whowechina/musec_pico/References/a-relic-of-the-past-museca-v0-1a24ue6pef9d1.webp

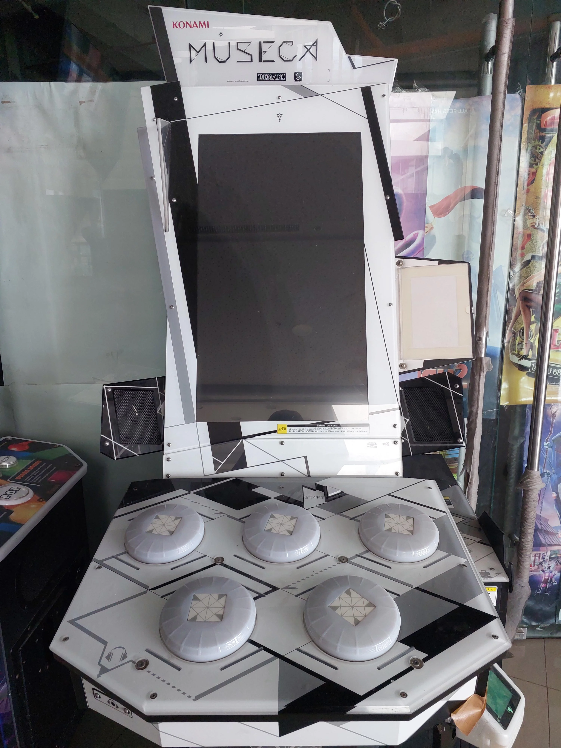
References/a-relic-of-the-past-museca-v0-1a24ue6pef9d1.webp
