whowechina/musec_pico/References/a-relic-of-the-past-museca-v0-k1ehcvuoef9d1.webp

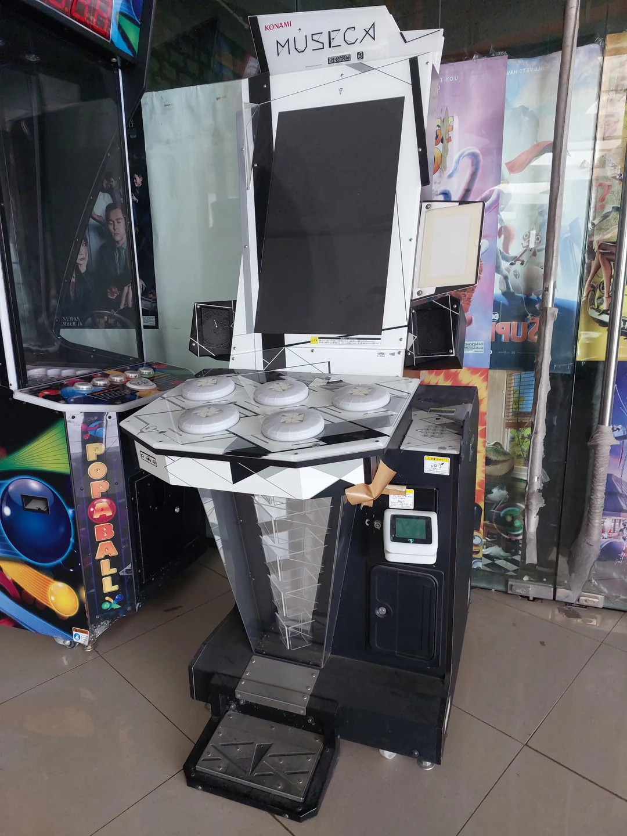
References/a-relic-of-the-past-museca-v0-k1ehcvuoef9d1.webp
