whowechina/musec_pico/References/museca-1.jpg

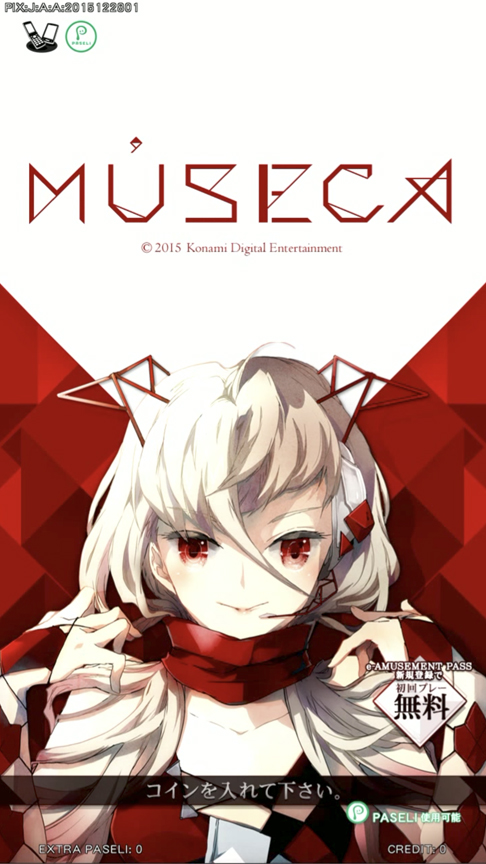
References/museca-1.jpg
