whowechina/musec_pico/Production/3DPrint/musec_pico+_pad.stl

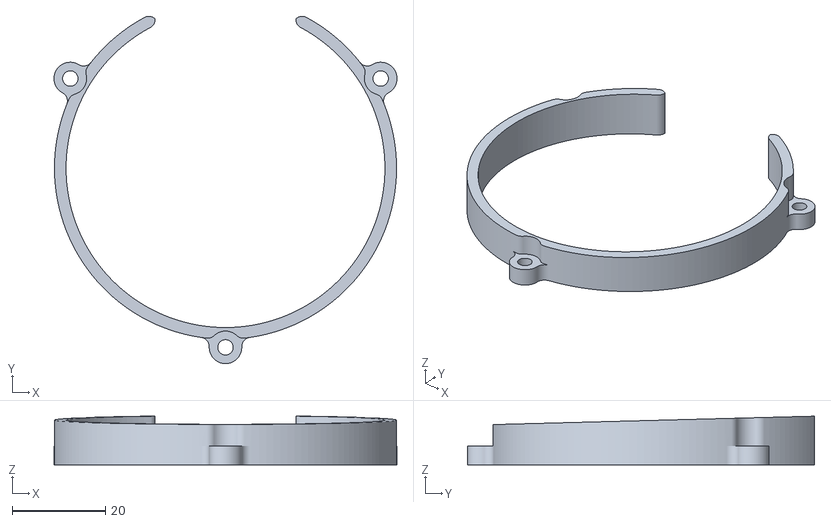
[picture p44: CAD file, 2025-05-17]
Production/3DPrint/musec_pico+_pad.stl
73.7 x 74.6 x 10.5
