whowechina/musec_pico/Production/3DPrint/musec_pico_bottom.stl

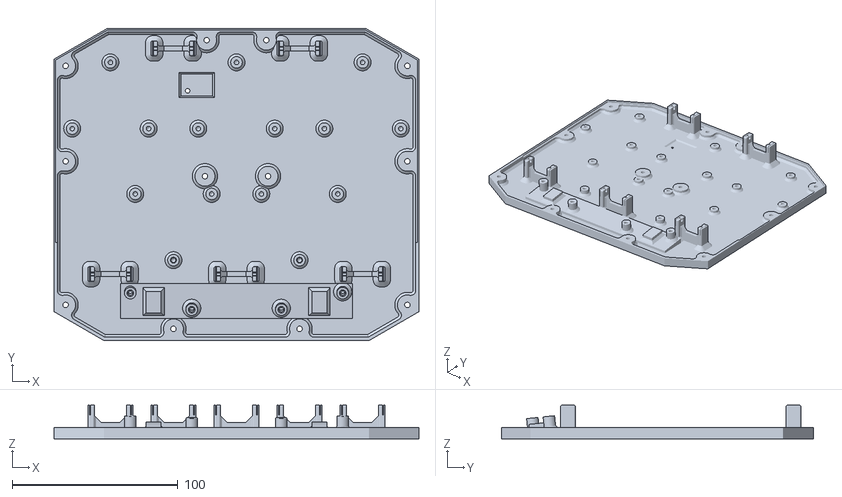
[picture p45: CAD file, 2024-10-18]
Production/3DPrint/musec_pico_bottom.stl
220.0 x 188.0 x 20.4
