whowechina/musec_pico/PCB/plus/3dmodels/SKPMAM.STEP

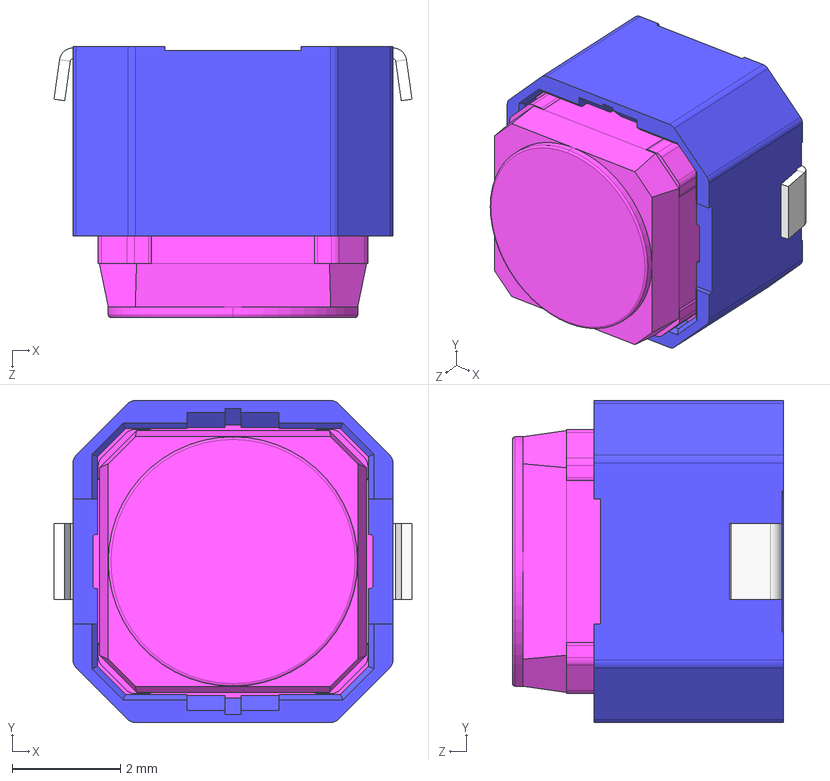
[picture p46: CAD file, 2025-05-04]
PCB/plus/3dmodels/SKPMAM.STEP
6.60 x 5.94 x 5.00 mm
