whowechina/musec_pico/Production/3DPrint/musec_pico_aux.stl

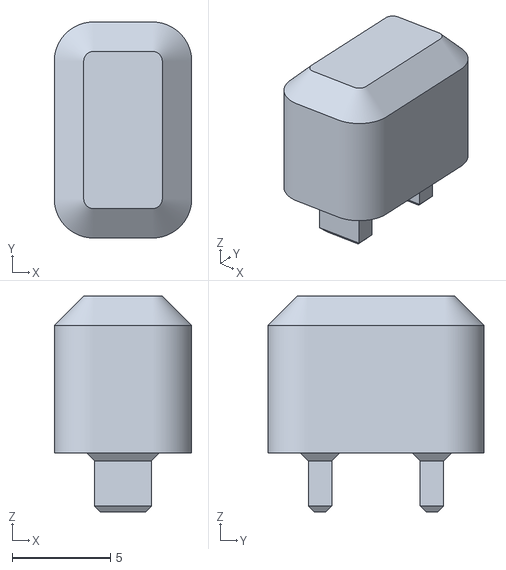
[picture p47: CAD file, 2024-10-16]
Production/3DPrint/musec_pico_aux.stl
7.00 x 11.0 x 11.0
