whowechina/musec_pico/PCB/plus/3dmodels/mpr121_breakout_v13.stl

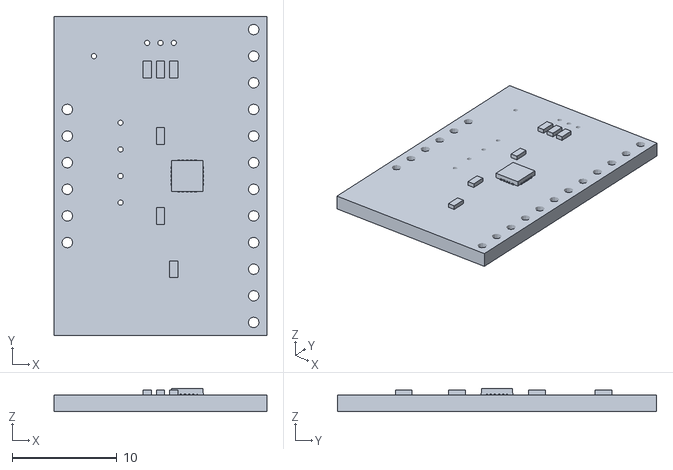
[picture p48: CAD file, 2025-05-04]
PCB/plus/3dmodels/mpr121_breakout_v13.stl
20.3 x 30.5 x 2.20
