whowechina/musec_pico/Production/3DPrint/musec_pico_shaft_end_7mm.stl

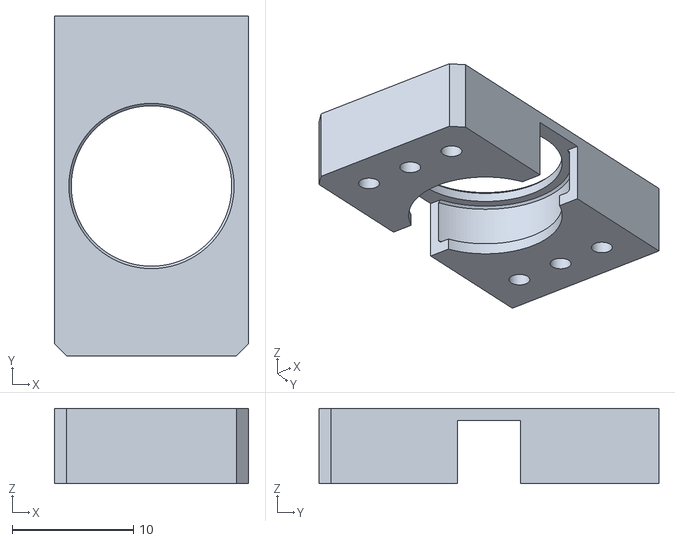
[picture p49: CAD file, 2024-10-16]
Production/3DPrint/musec_pico_shaft_end_7mm.stl
16.0 x 28.0 x 6.20
