whowechina/musec_pico/PCB/plus/3dmodels/EVQ-P1D05M.stp

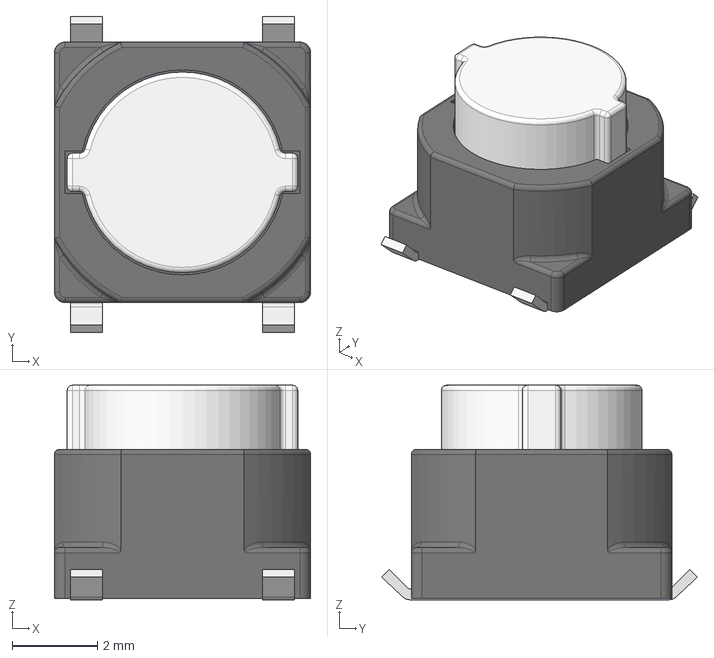
[picture p50: CAD file, 2025-05-04]
PCB/plus/3dmodels/EVQ-P1D05M.stp
6.00 x 7.40 x 5.03 mm
