whowechina/musec_pico/Production/3DPrint/musec_pico_shaft_end_6mm.stl

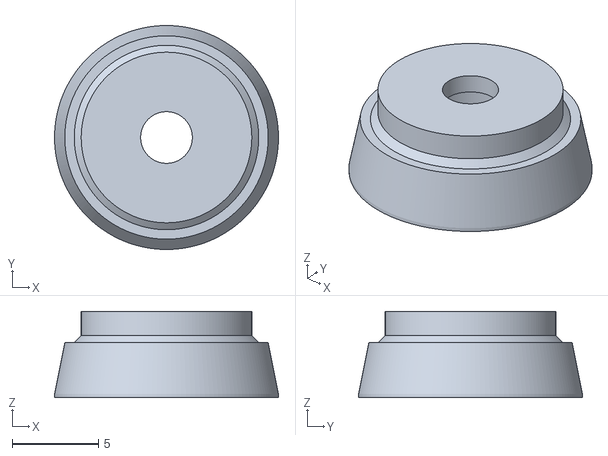
[picture p51: CAD file, 2024-10-16]
Production/3DPrint/musec_pico_shaft_end_6mm.stl
13.0 x 13.0 x 5.00
