whowechina/musec_pico/Production/3DPrint/musec_pico_pedal.stl

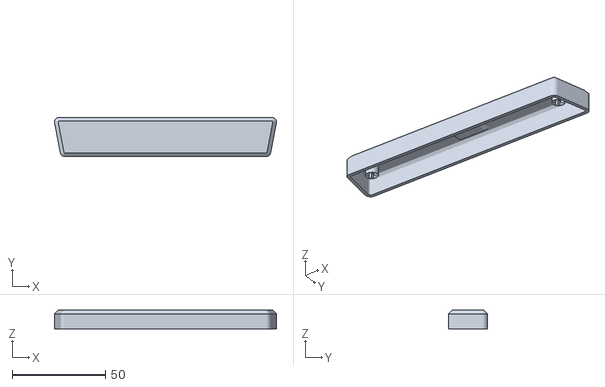
[picture p53: CAD file, 2024-10-16]
Production/3DPrint/musec_pico_pedal.stl
119.0 x 21.0 x 10.0
