whowechina/musec_pico/PCB/plus/3dmodels/SKSTAAE010.stp

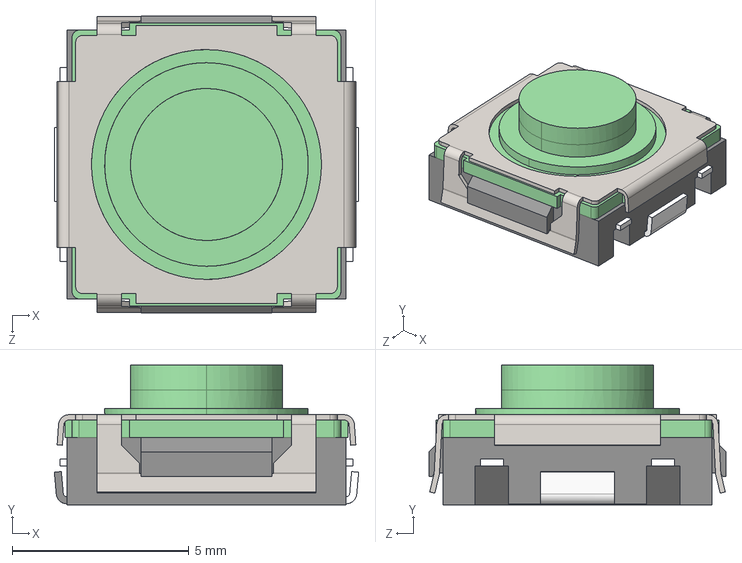
[picture p54: CAD file, 2025-05-04]
PCB/plus/3dmodels/SKSTAAE010.stp
8.61 x 3.95 x 8.40 mm
