whowechina/musec_pico/PCB/plus/3dmodels/Kailh_PG1353.STEP

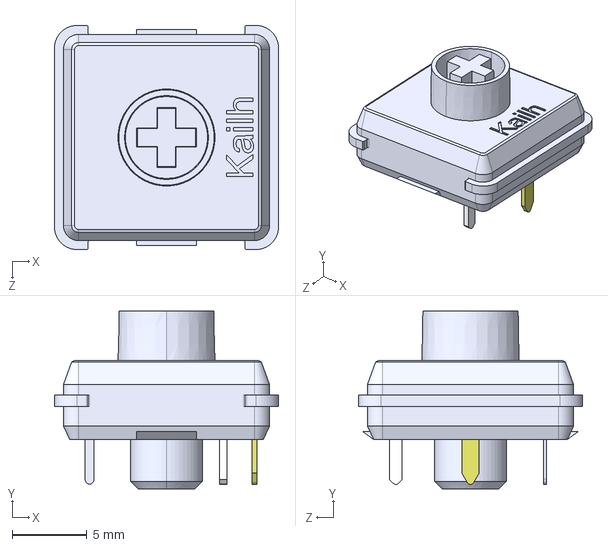
[picture p55: CAD file, 2025-05-04]
PCB/plus/3dmodels/Kailh_PG1353.STEP
15.0 x 11.9 x 15.0 mm
