whowechina/musec_pico/PCB/plus/3dmodels/User Library-RGB1204.STEP

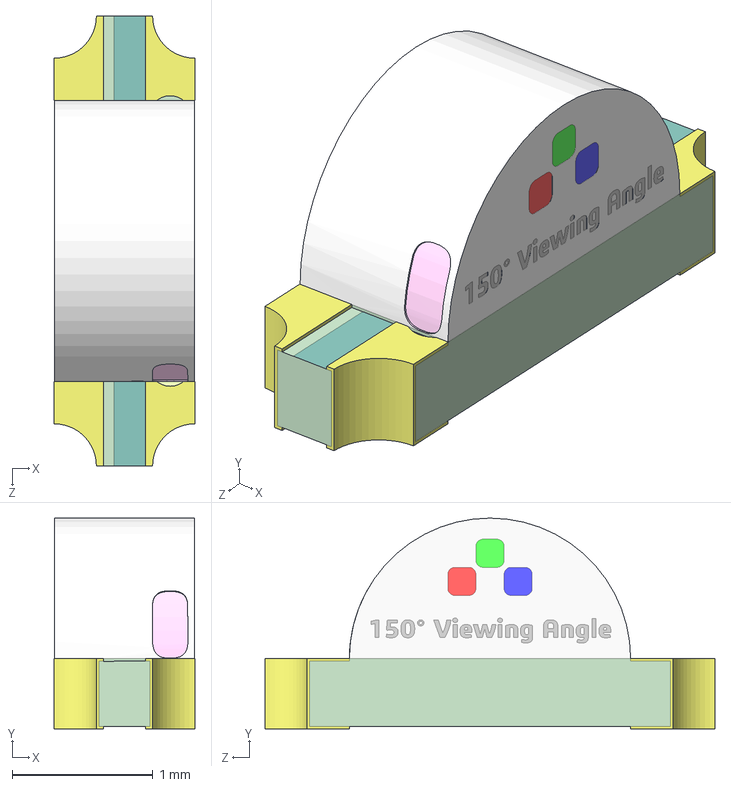
[picture p56: CAD file, 2025-05-04]
PCB/plus/3dmodels/User Library-RGB1204.STEP
1.00 x 1.50 x 3.20 mm
