whowechina/musec_pico/PCB/plus/3dmodels/SW_Hotswap_Kailh_Choc_V1.stp

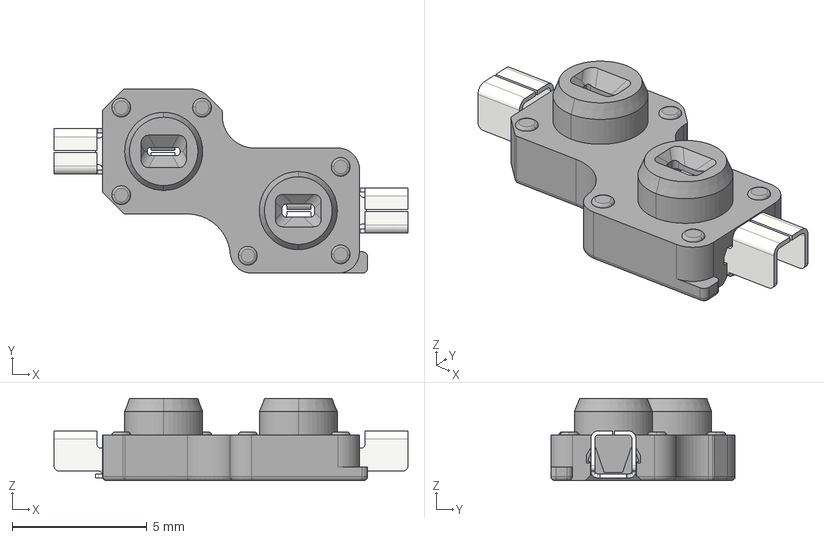
[picture p57: CAD file, 2024-09-26]
PCB/plus/3dmodels/SW_Hotswap_Kailh_Choc_V1.stp
13.2 x 6.85 x 3.05 mm
