whowechina/musec_pico/PCB/plus/3dmodels/keypad_lgp.3mf

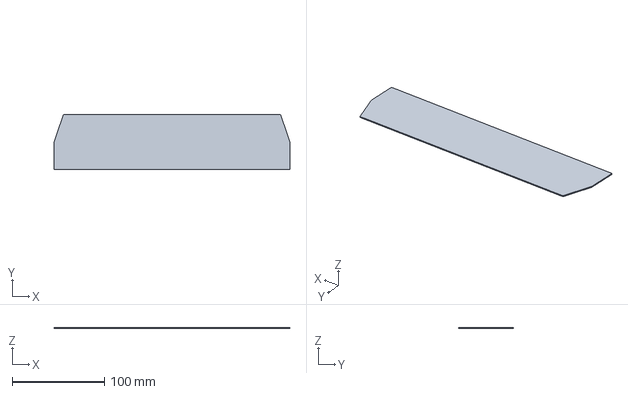
[picture p58: CAD file, 2024-09-26]
PCB/plus/3dmodels/keypad_lgp.3mf
256.0 x 60.0 x 1.00 mm
