whowechina/musec_pico/PCB/plus/3dmodels/Magnetic Pogo Connector 5 Pin (Type 2).STEP

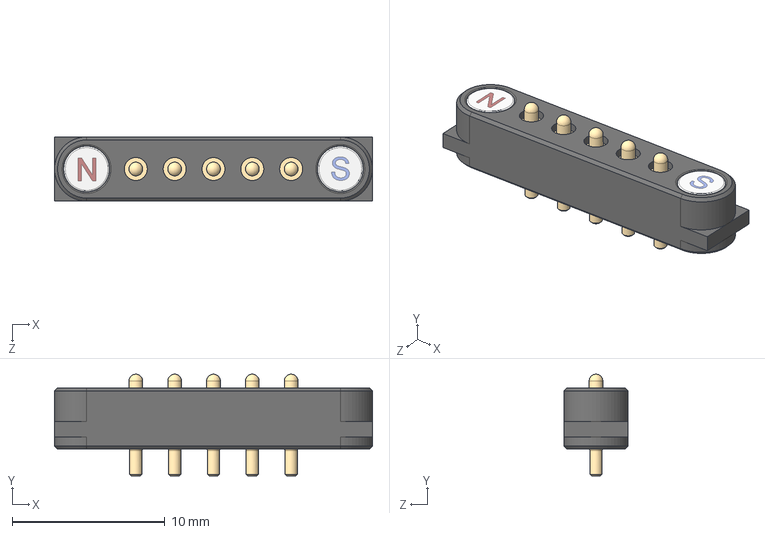
[picture p59: CAD file, 2024-09-26]
PCB/plus/3dmodels/Magnetic Pogo Connector 5 Pin (Type 2).STEP
20.8 x 6.65 x 4.20 mm
