whowechina/musec_pico/PCB/plus/3dmodels/Magnetic Pogo Connector 5 Pin (Type 3).STEP

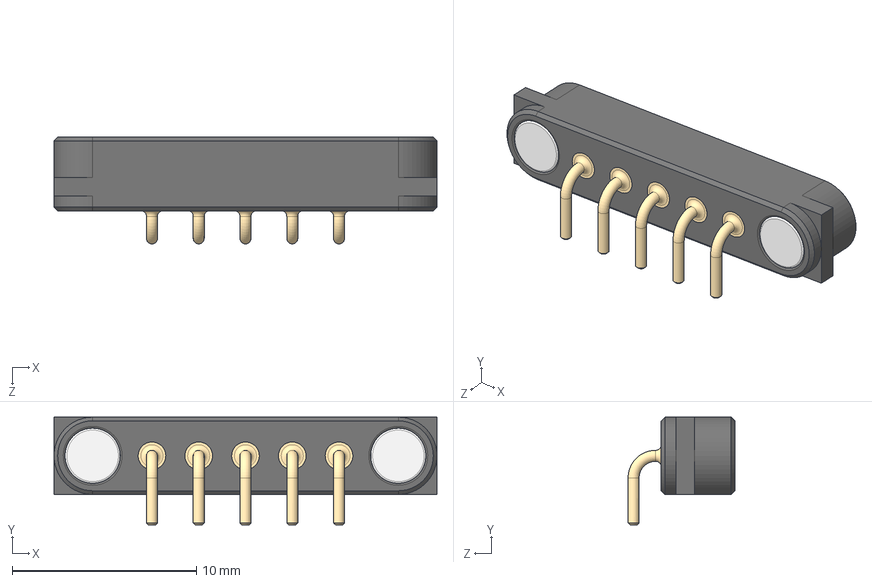
[picture p60: CAD file, 2024-09-26]
PCB/plus/3dmodels/Magnetic Pogo Connector 5 Pin (Type 3).STEP
20.8 x 5.85 x 5.80 mm
