whowechina/musec_pico/PCB/plus/3dmodels/SW_Kailh_Choc_V1.stp

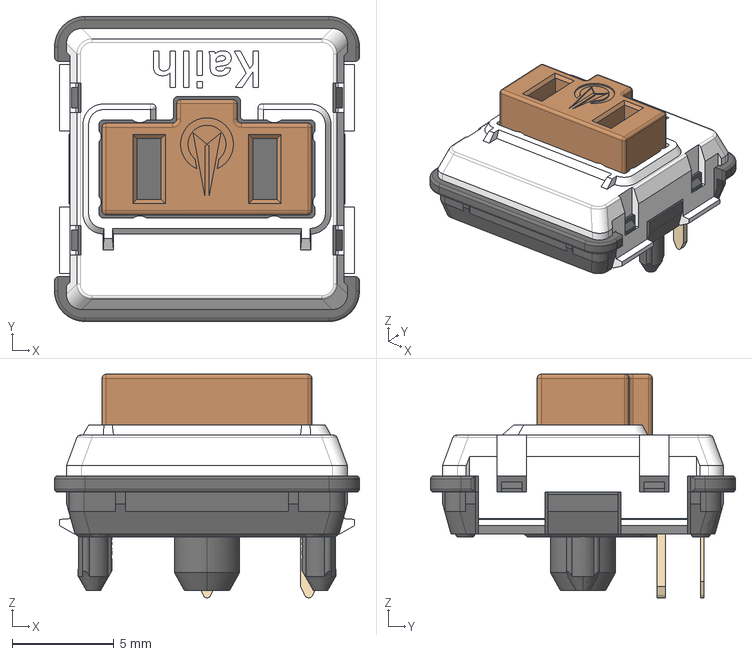
[picture p61: CAD file, 2024-09-26]
PCB/plus/3dmodels/SW_Kailh_Choc_V1.stp
15.0 x 15.0 x 11.0 mm
