whowechina/musec_pico/PCB/plus/3dmodels/8002A.step

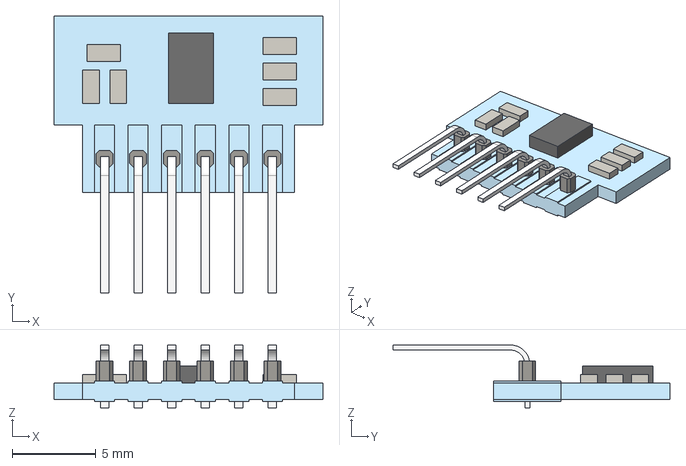
[picture p62: CAD file, 2024-09-26]
PCB/plus/3dmodels/8002A.step
16.0 x 16.5 x 3.75 mm
