whowechina/musec_pico/PCB/plus/3dmodels/WS2812B.step

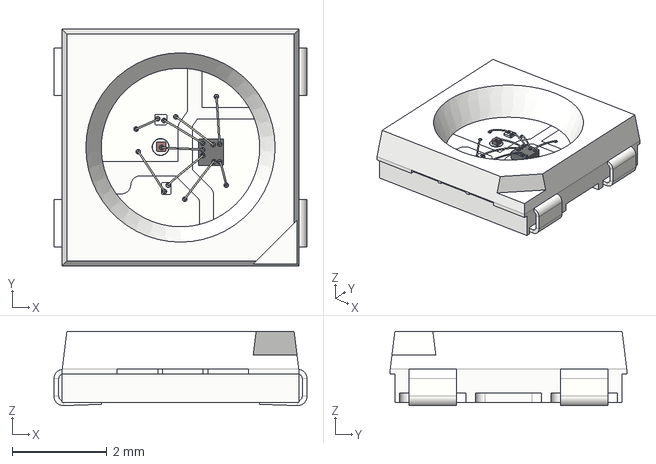
[picture p63: CAD file, 2024-09-26]
PCB/plus/3dmodels/WS2812B.step
5.35 x 5.00 x 1.57 mm
