whowechina/musec_pico/PCB/plus/3dmodels/geki_button.step

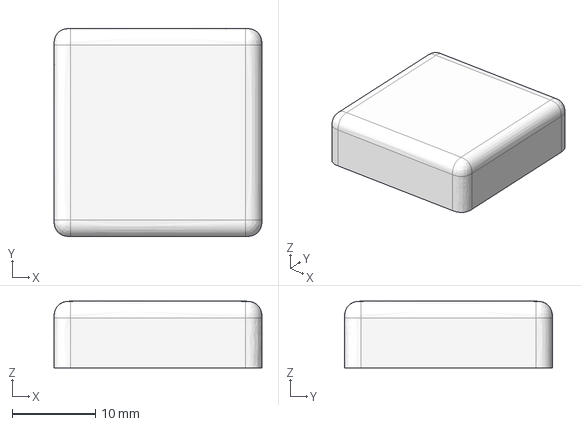
[picture p64: CAD file, 2024-09-26]
PCB/plus/3dmodels/geki_button.step
25.0 x 25.0 x 8.00 mm
