whowechina/musec_pico/PCB/plus/3dmodels/chu_keypad_lgp.step

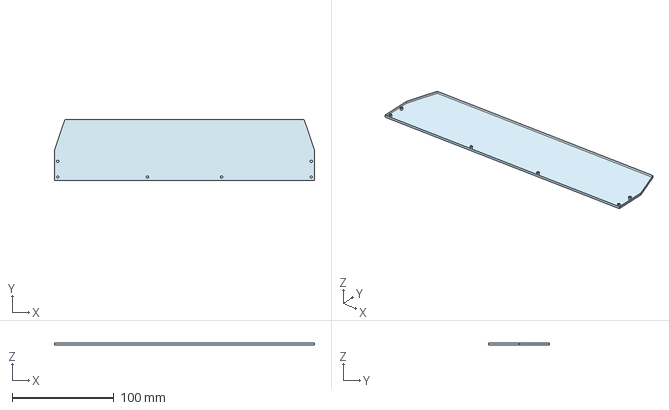
[picture p65: CAD file, 2024-09-26]
PCB/plus/3dmodels/chu_keypad_lgp.step
256.0 x 60.0 x 2.00 mm
