whowechina/musec_pico/PCB/plus/3dmodels/dcdc_3to5.step

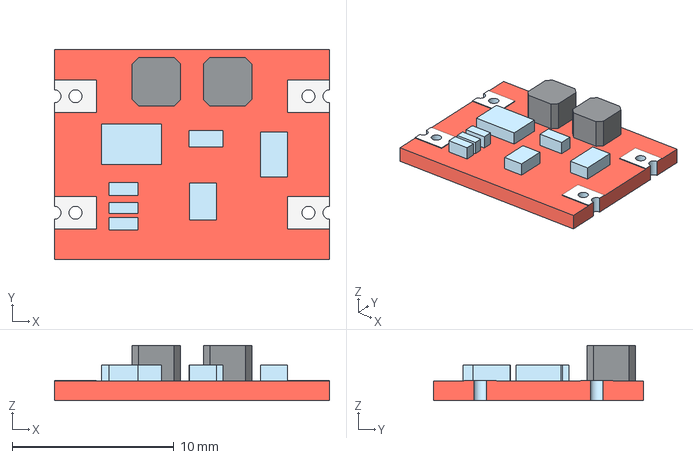
[picture p66: CAD file, 2024-09-26]
PCB/plus/3dmodels/dcdc_3to5.step
17.0 x 13.0 x 3.40 mm
