whowechina/musec_pico/PCB/plus/3dmodels/WS2812-2020.STEP

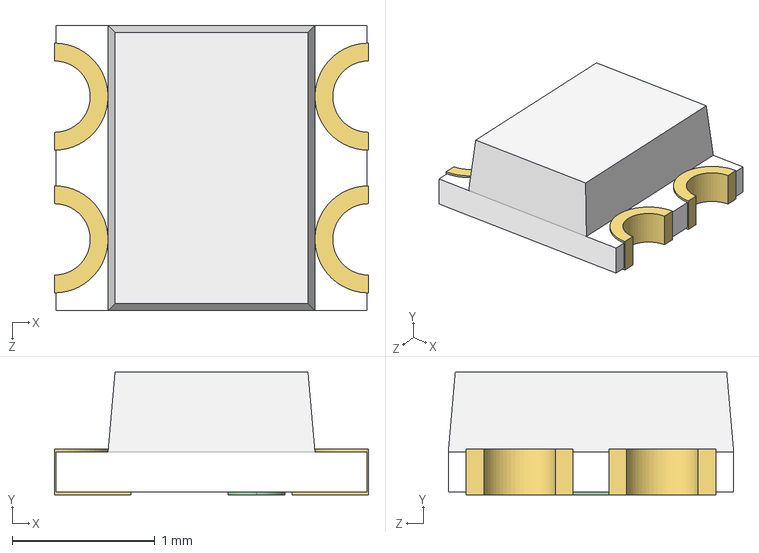
[picture p67: CAD file, 2024-09-26]
PCB/plus/3dmodels/WS2812-2020.STEP
2.20 x 0.86 x 2.00 mm
