whowechina/musec_pico/PCB/plus/3dmodels/J 2835.step

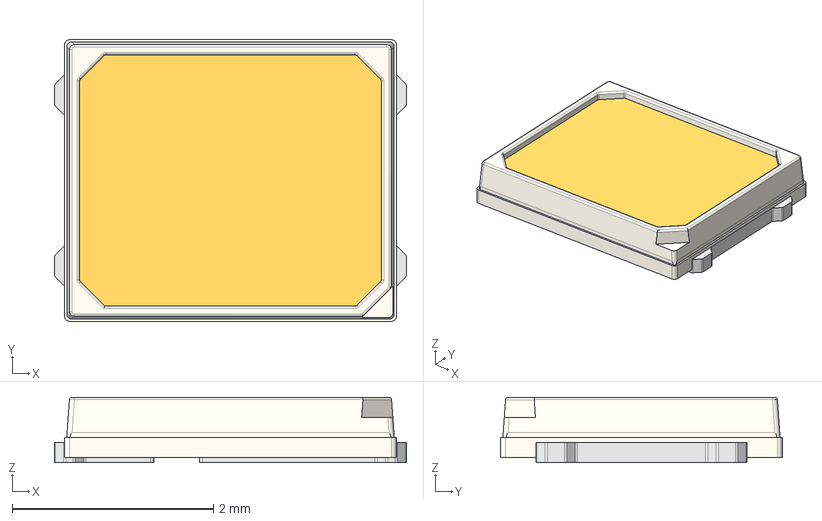
[picture p68: CAD file, 2024-09-26]
PCB/plus/3dmodels/J 2835.step
3.50 x 2.80 x 0.65 mm
