whowechina/musec_pico/PCB/plus/3dmodels/Kailh LP Choc PC Keycap.step

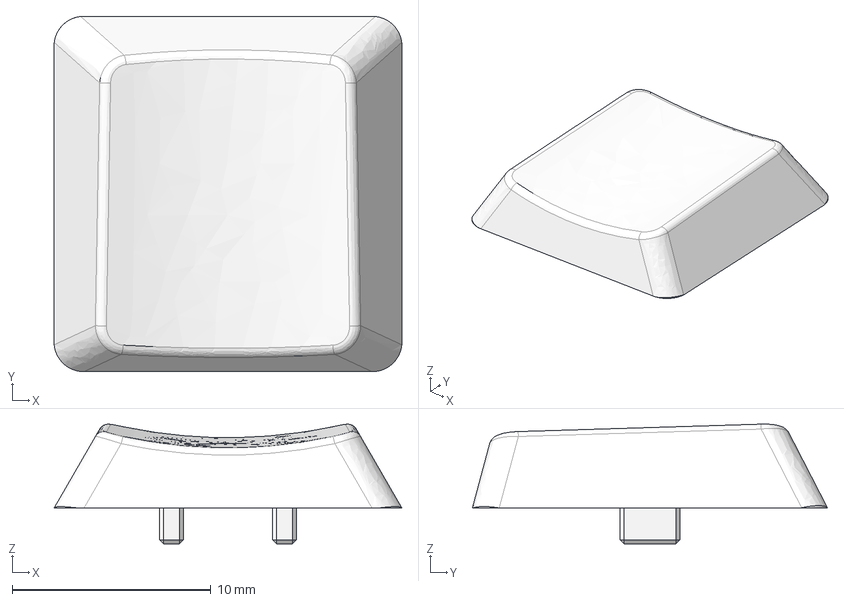
[picture p70: CAD file, 2024-09-26]
PCB/plus/3dmodels/Kailh LP Choc PC Keycap.step
17.5 x 17.9 x 6.03 mm
