whowechina/musec_pico/PCB/plus/3dmodels/SW_Hotswap_Kailh_MX.stp

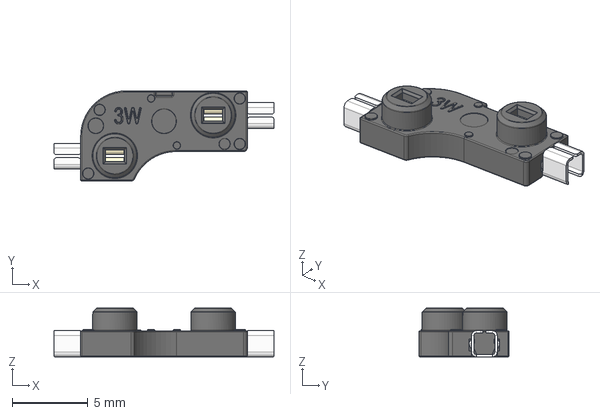
[picture p71: CAD file, 2024-09-26]
PCB/plus/3dmodels/SW_Hotswap_Kailh_MX.stp
14.5 x 5.95 x 3.22 mm
