whowechina/musec_pico/PCB/plus/3dmodels/Magnetic Pogo Connector 5 Pin (F).STEP

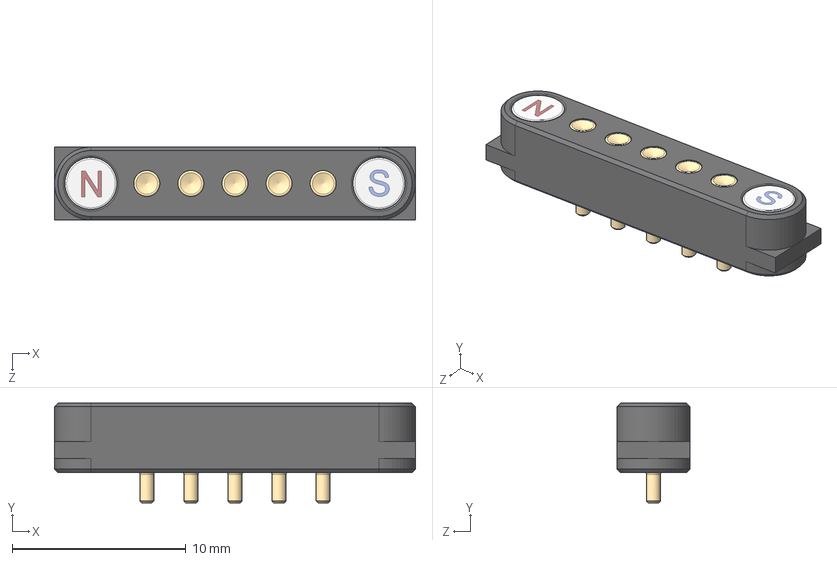
[picture p73: CAD file, 2024-09-26]
PCB/plus/3dmodels/Magnetic Pogo Connector 5 Pin (F).STEP
20.8 x 5.75 x 4.20 mm
