whowechina/musec_pico/PCB/plus/3dmodels/Tact Switch 4.5mm SMT.step

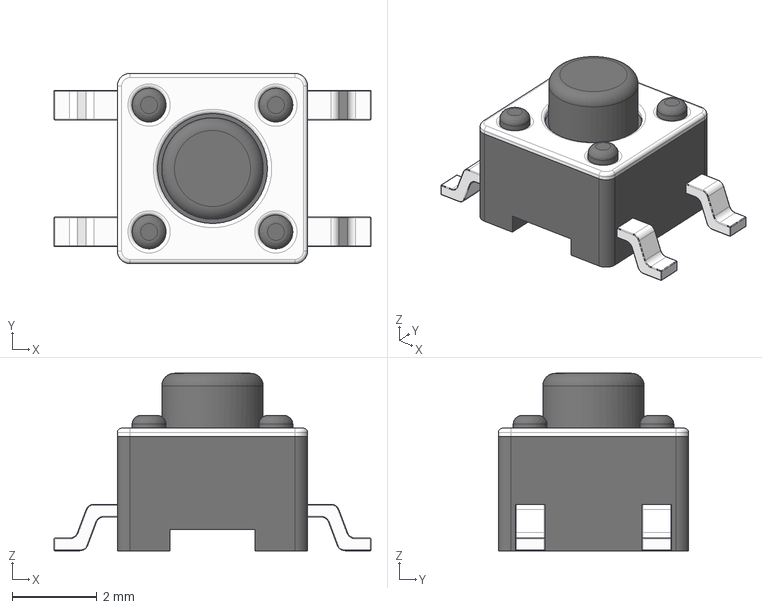
[picture p74: CAD file, 2024-09-26]
PCB/plus/3dmodels/Tact Switch 4.5mm SMT.step
7.50 x 4.50 x 4.20 mm
