whowechina/musec_pico/PCB/plus/3dmodels/SS49E.step

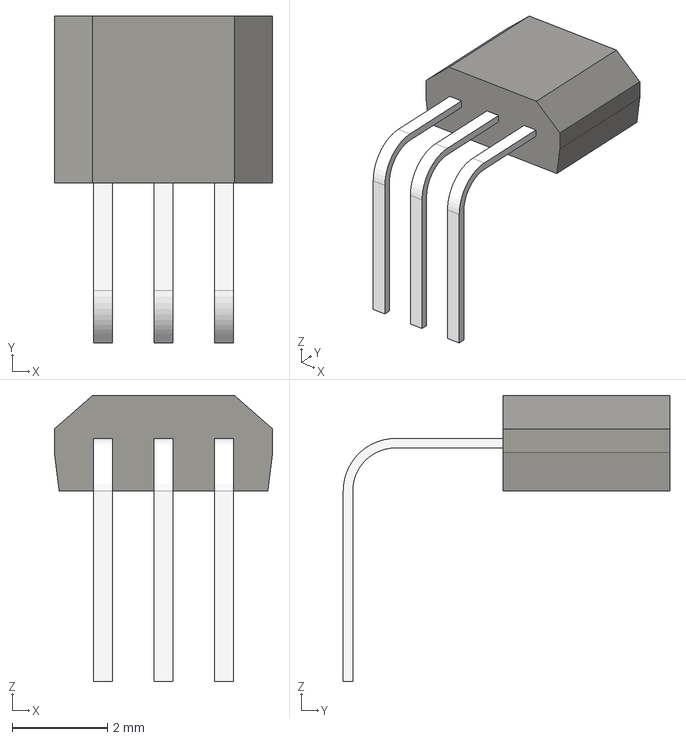
[picture p75: CAD file, 2024-09-26]
PCB/plus/3dmodels/SS49E.step
4.58 x 6.85 x 6.00 mm
