whowechina/musec_pico/PCB/plus/3dmodels/User Library-WS2812-2020.step

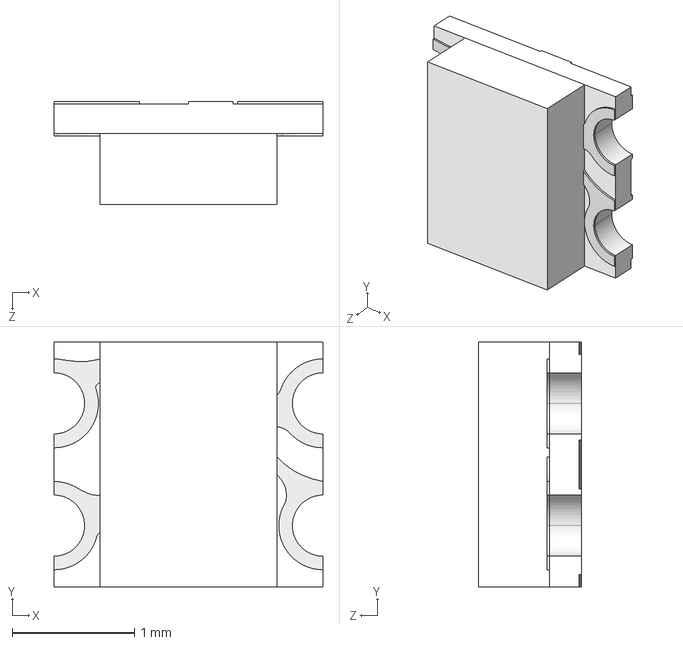
[picture p76: CAD file, 2024-09-26]
PCB/plus/3dmodels/User Library-WS2812-2020.step
2.20 x 2.00 x 0.84 mm
