whowechina/musec_pico/PCB/plus/3dmodels/Button Cap.step

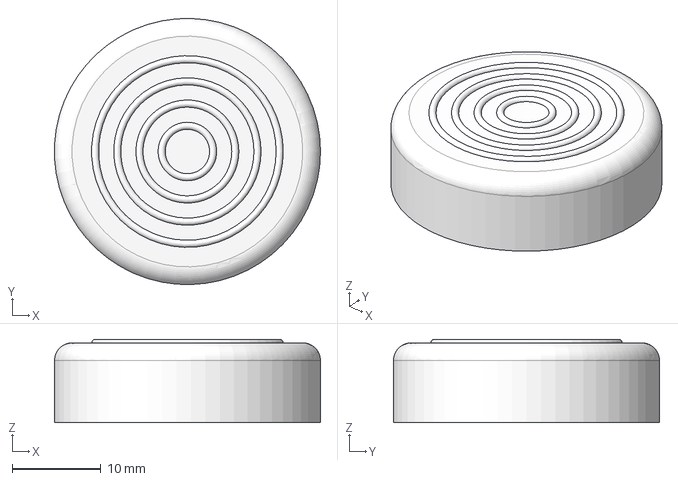
[picture p77: CAD file, 2024-09-26]
PCB/plus/3dmodels/Button Cap.step
30.0 x 30.0 x 9.40 mm
