whowechina/musec_pico/PCB/plus/3dmodels/pn5180.step

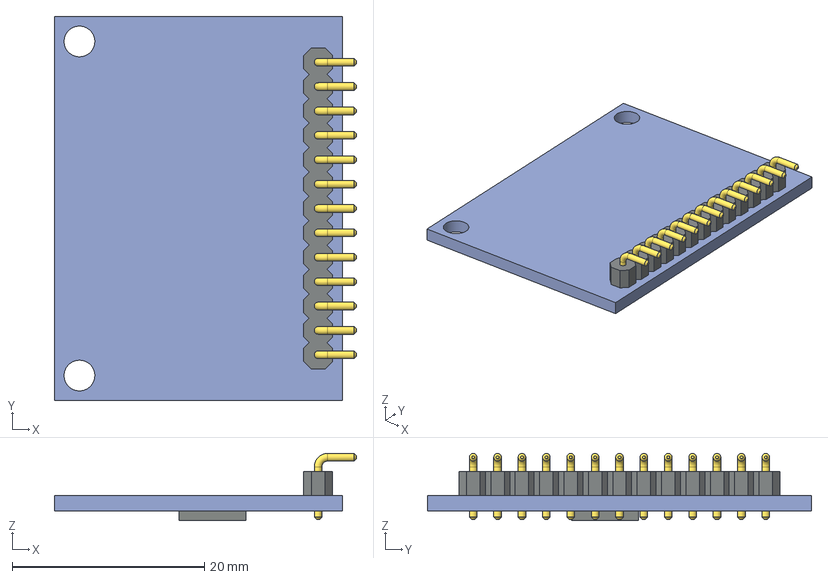
[picture p78: CAD file, 2024-09-26]
PCB/plus/3dmodels/pn5180.step
31.5 x 40.0 x 7.00 mm
