whowechina/musec_pico/PCB/plus/3dmodels/Slider.step

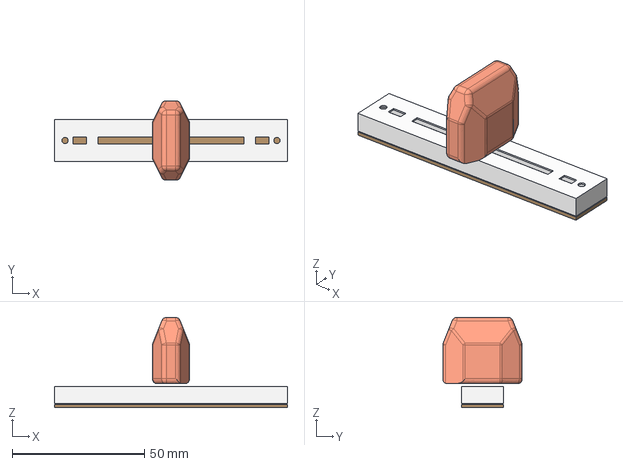
[picture p79: CAD file, 2024-09-26]
PCB/plus/3dmodels/Slider.step
88.0 x 30.0 x 34.0 mm
