whowechina/musec_pico/PCB/plus/3dmodels/Geki_Slider.step

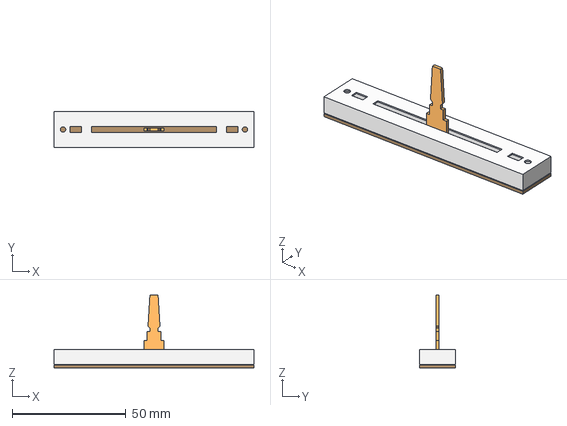
[picture p82: CAD file, 2024-09-26]
PCB/plus/3dmodels/Geki_Slider.step
88.0 x 16.0 x 32.0 mm
